Mona-zza/key-bowwrd/Images/Screenshot5.png

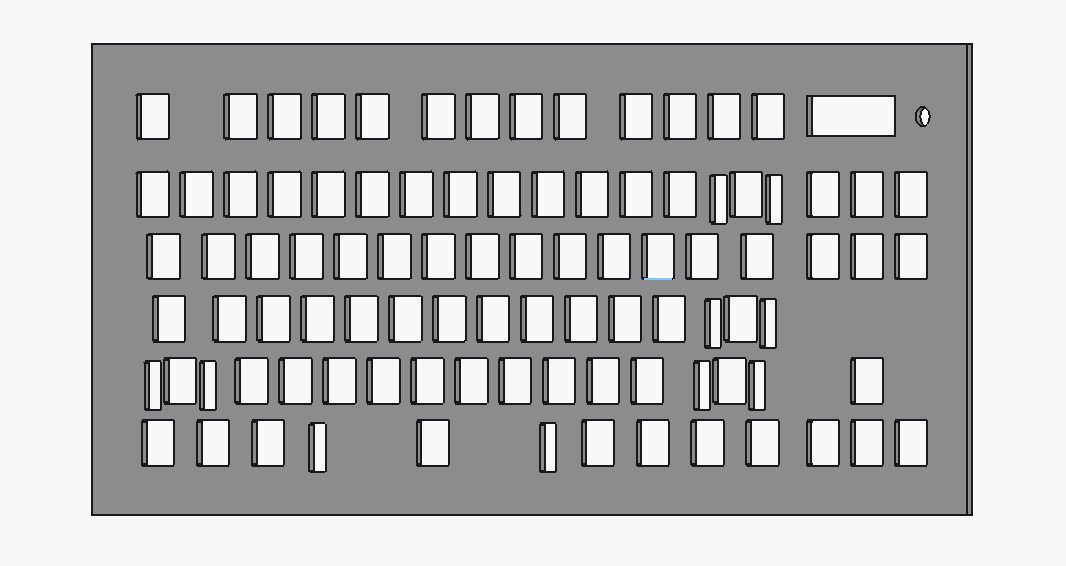
Images/Screenshot5.png
